gnargle/RinaChanBoard/Images/IMG_20210302_183425__01.jpg

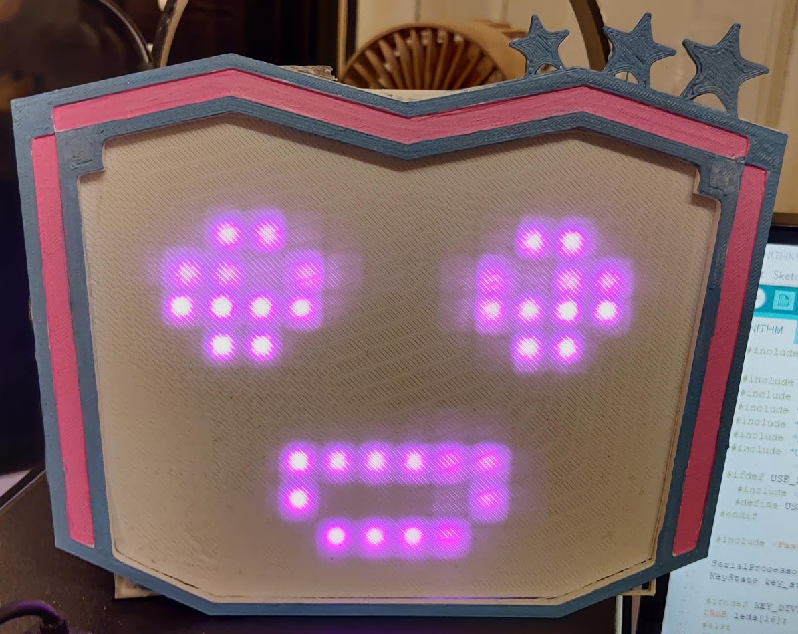
Images/IMG_20210302_183425__01.jpg
